Sai1833/Smart-Pill-Box-IoT/01-Simulations/Circuit_Design.jpeg

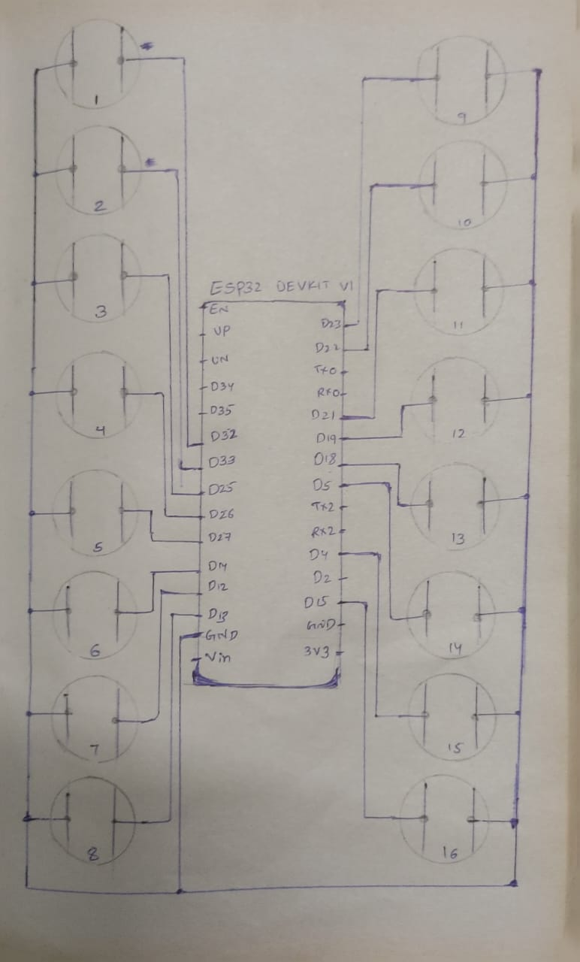
01-Simulations/Circuit_Design.jpeg
