Sai1833/Smart-Pill-Box-IoT/01-Simulations/IR_Simulation.jpeg

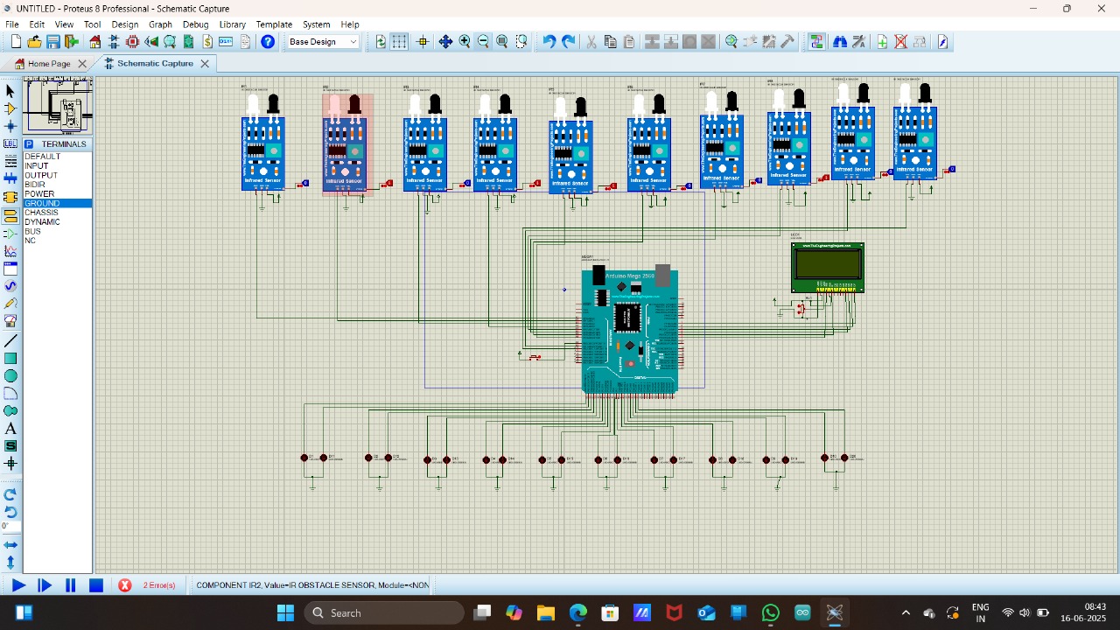
01-Simulations/IR_Simulation.jpeg
