Sai1833/Smart-Pill-Box-IoT/01-Simulations/Touch_Sensor_Simulation.jpeg

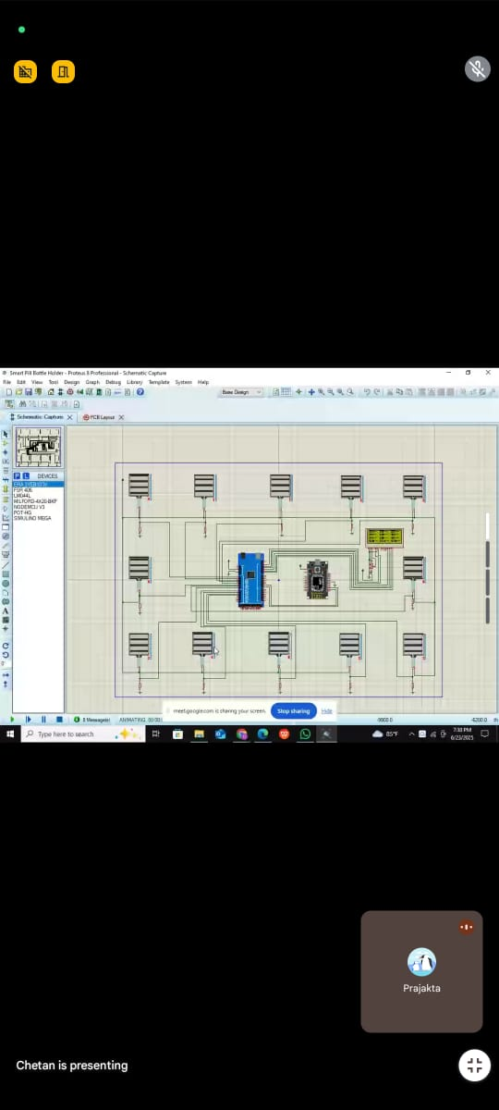
01-Simulations/Touch_Sensor_Simulation.jpeg
