Sai1833/Smart-Pill-Box-IoT/02-Prototype/Cardboard_prototype_1.jpeg

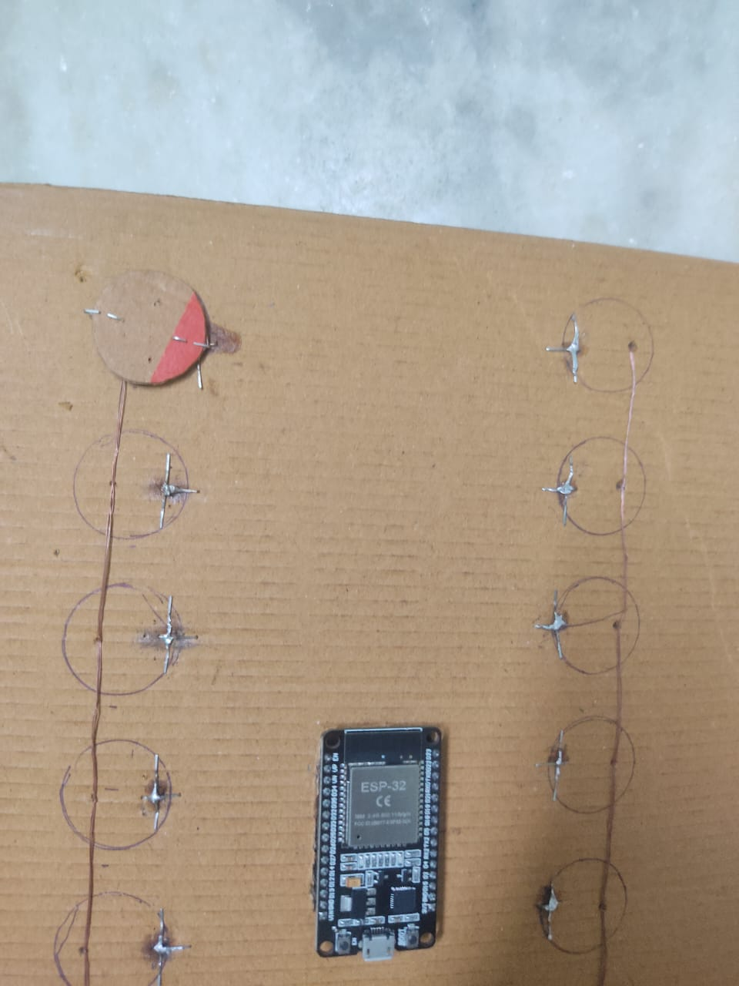
02-Prototype/Cardboard_prototype_1.jpeg
