Sai1833/Smart-Pill-Box-IoT/02-Prototype/Cardboard_prototype_2.jpeg

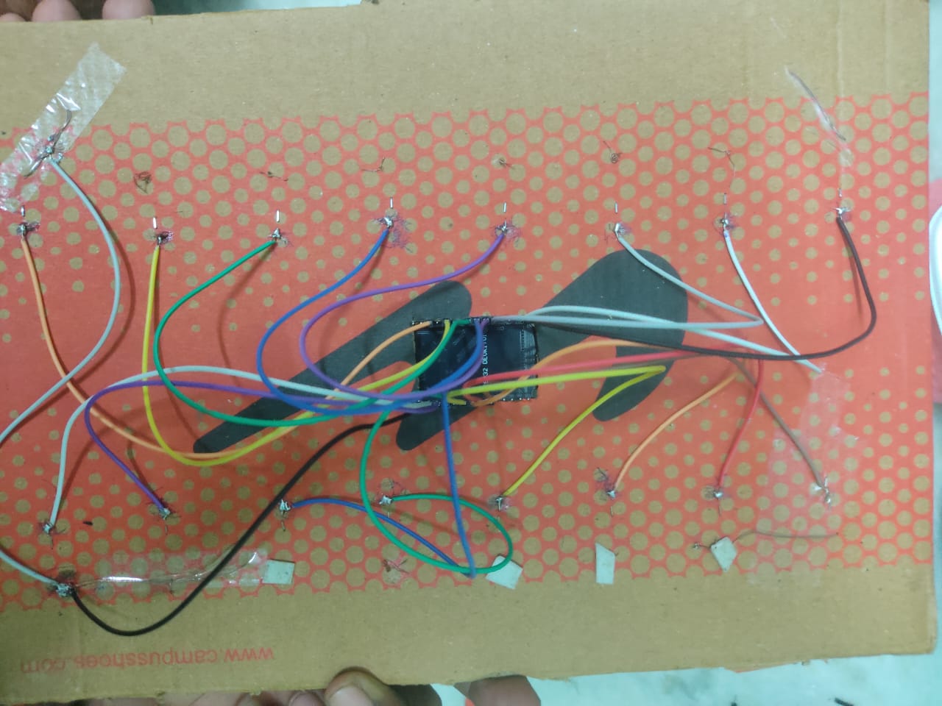
02-Prototype/Cardboard_prototype_2.jpeg
