Sai1833/Smart-Pill-Box-IoT/02-Prototype/Prototype_output.jpeg

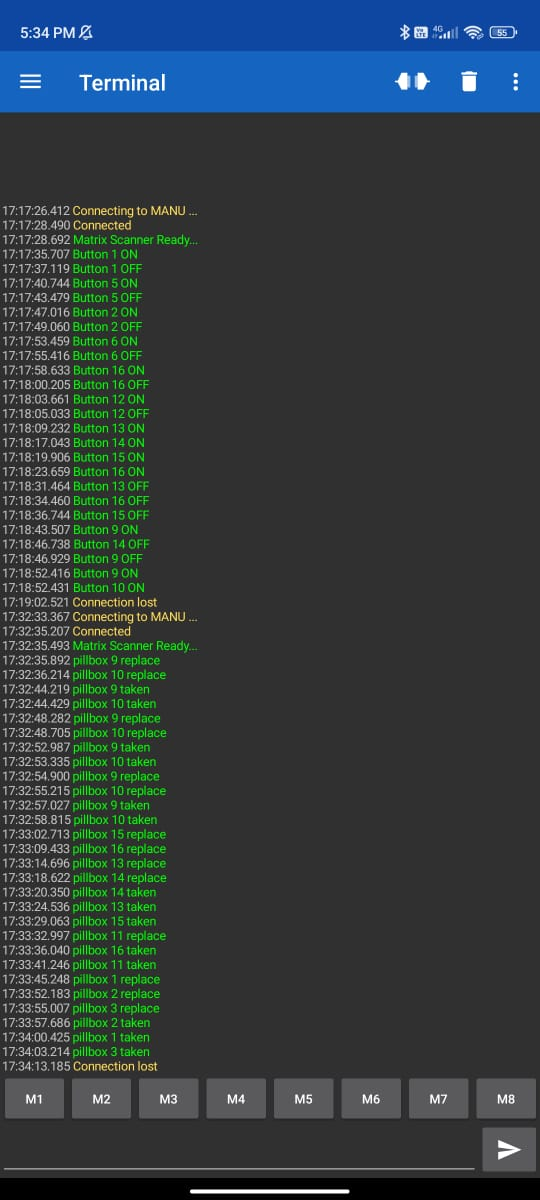
02-Prototype/Prototype_output.jpeg
