Sai1833/Smart-Pill-Box-IoT/02-Prototype/Reference_model.jpeg

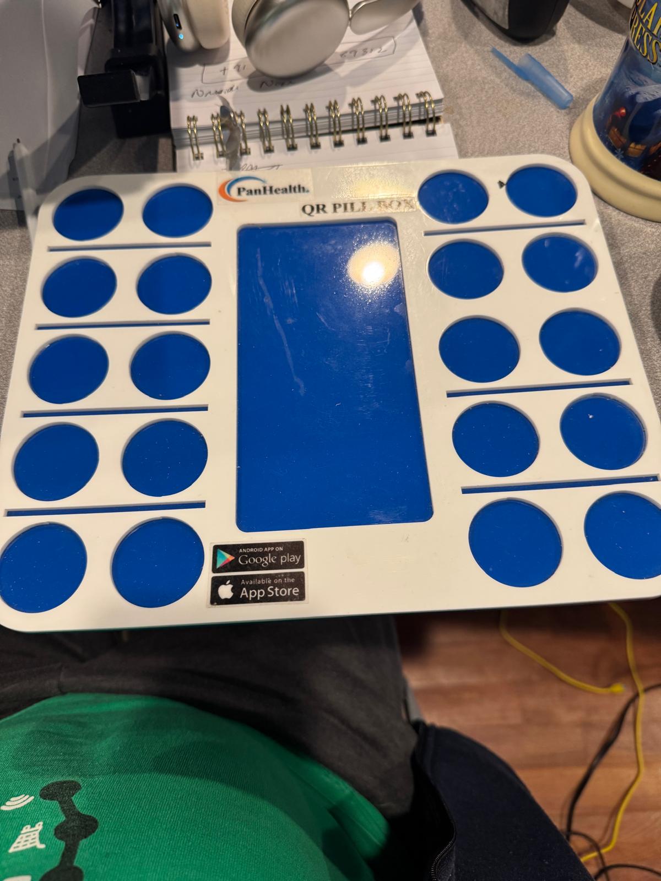
02-Prototype/Reference_model.jpeg
