Sai1833/Smart-Pill-Box-IoT/03-PCB_Design/PCB_Hardware/FeCl3_Mixing_img01.jpg

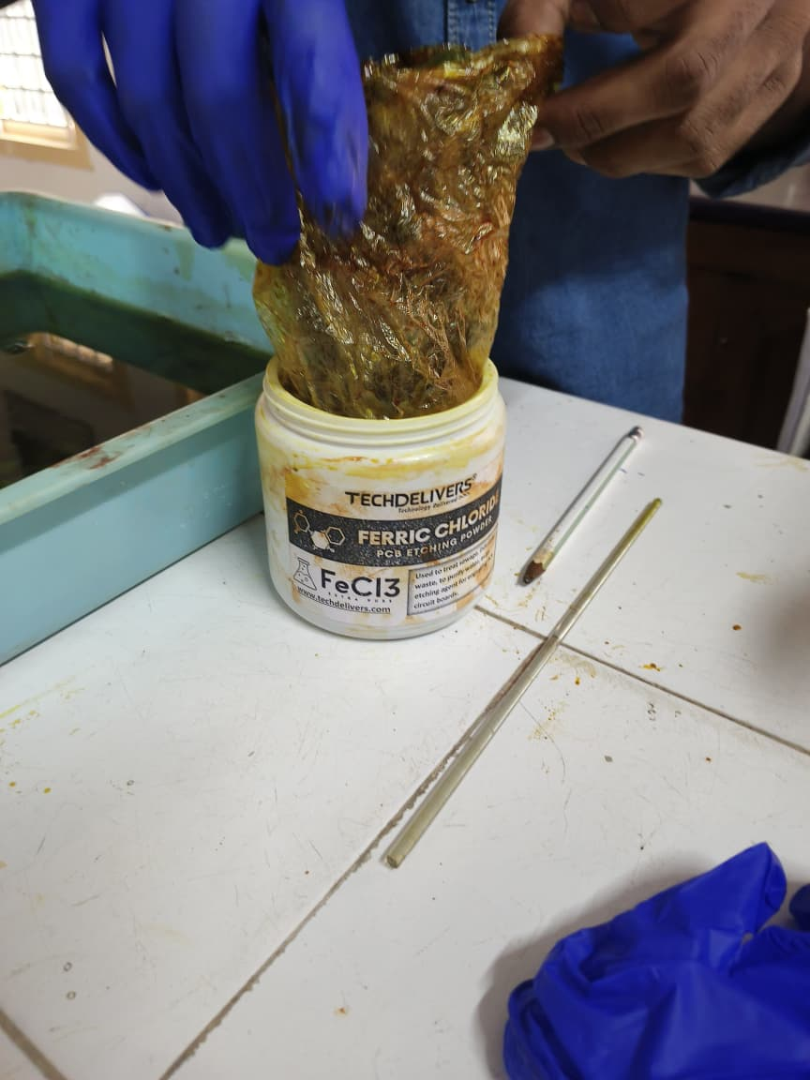
03-PCB_Design/PCB_Hardware/FeCl3_Mixing_img01.jpg
