Sai1833/Smart-Pill-Box-IoT/03-PCB_Design/PCB_Hardware/PCB_Before_Removing_Copper_img01.jpg

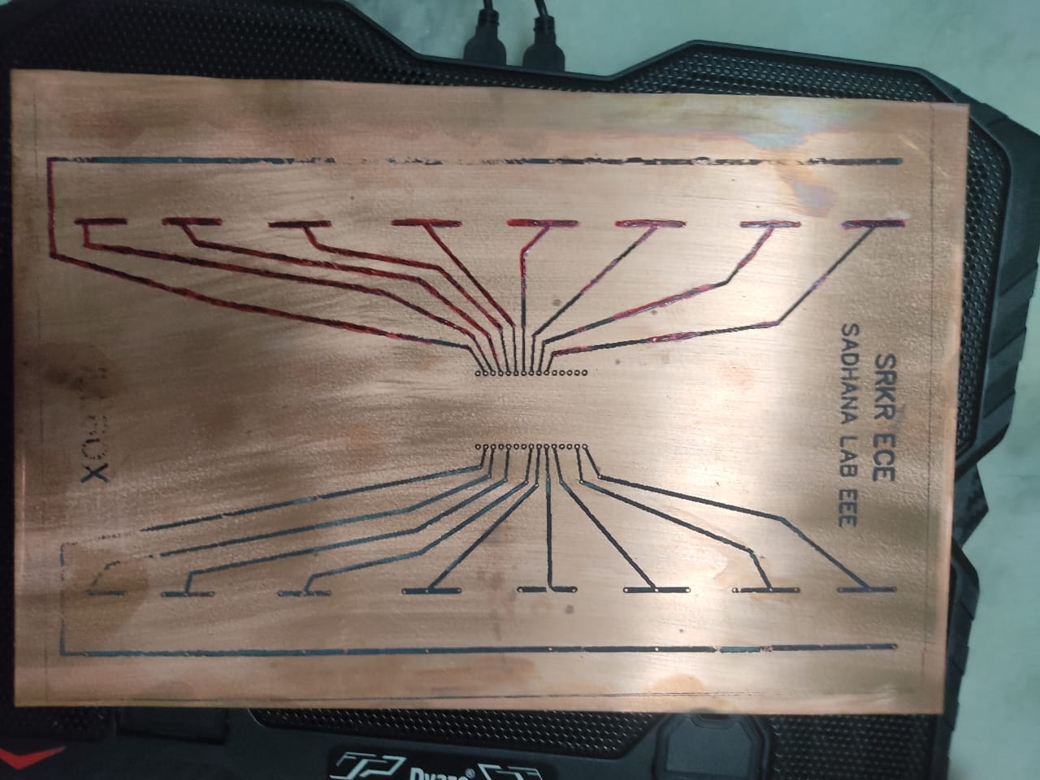
03-PCB_Design/PCB_Hardware/PCB_Before_Removing_Copper_img01.jpg
