Sai1833/Smart-Pill-Box-IoT/03-PCB_Design/PCB_Hardware/PCB_with_Sholdered_MC_img03.jpg

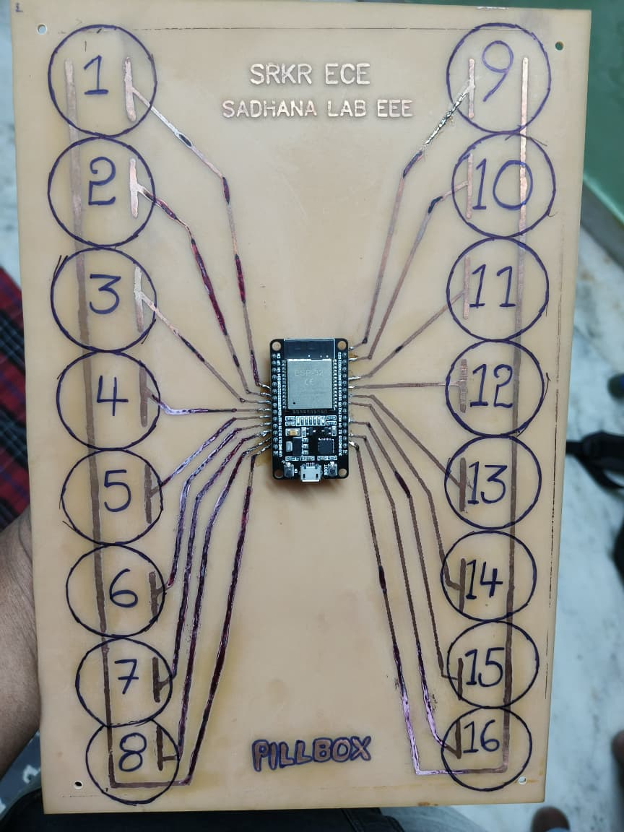
03-PCB_Design/PCB_Hardware/PCB_with_Sholdered_MC_img03.jpg
