Sai1833/Smart-Pill-Box-IoT/03-PCB_Design/PCB_Simulation/PCB_Design_EasyEda_img02.jpg

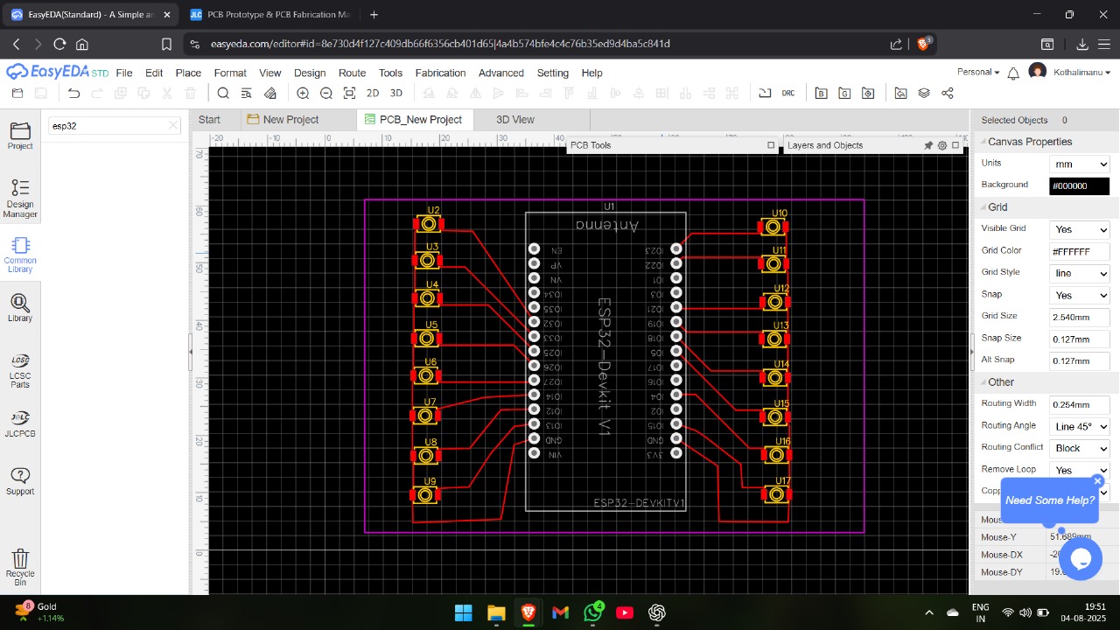
03-PCB_Design/PCB_Simulation/PCB_Design_EasyEda_img02.jpg
