Sai1833/Smart-Pill-Box-IoT/04-3D_Design/Autocad_3D_Design_Top&Bottle_img01.jpg

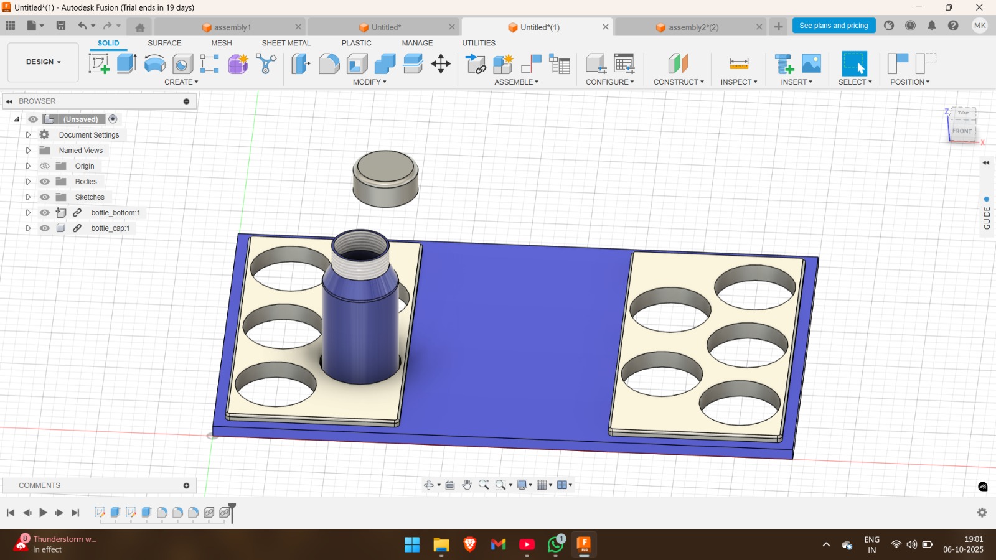
04-3D_Design/Autocad_3D_Design_Top&Bottle_img01.jpg
