Sai1833/Smart-Pill-Box-IoT/04-3D_Design/Autocad_3D_Design_Top_img02.jpg

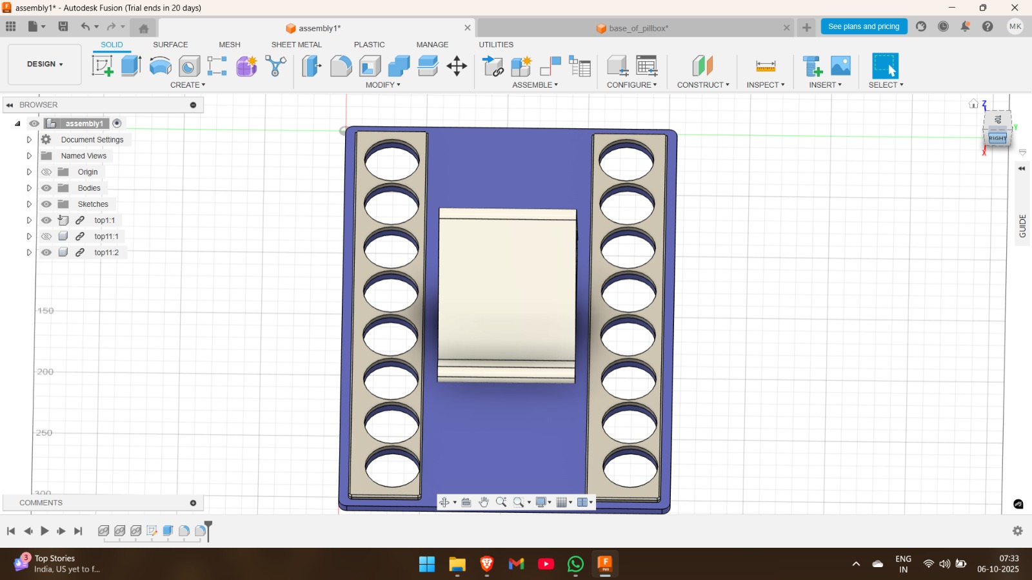
04-3D_Design/Autocad_3D_Design_Top_img02.jpg
