Sai1833/Smart-Pill-Box-IoT/05-Final_output/Final_Output_Insidebox_img03.jpg

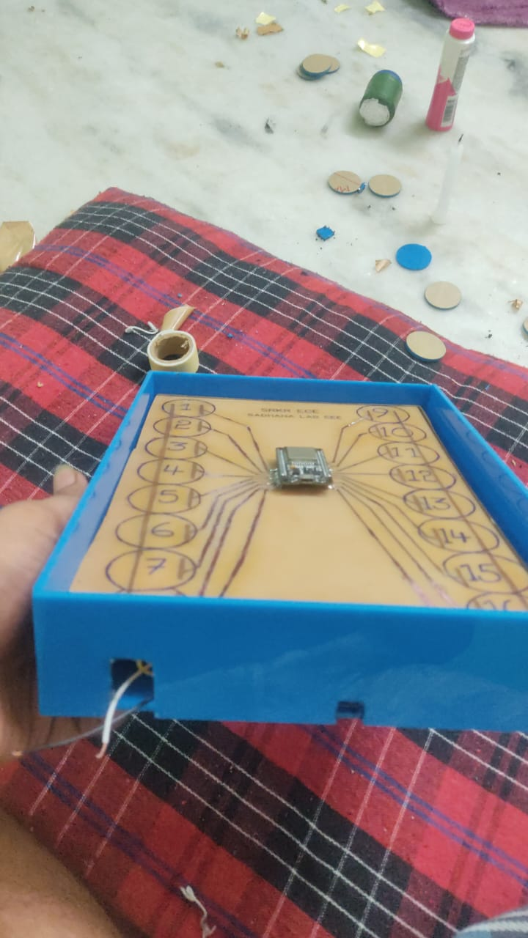
05-Final_output/Final_Output_Insidebox_img03.jpg
