Sai1833/Smart-Pill-Box-IoT/05-Final_output/Outlet_Box_Laser_Cutting_img01.jpg

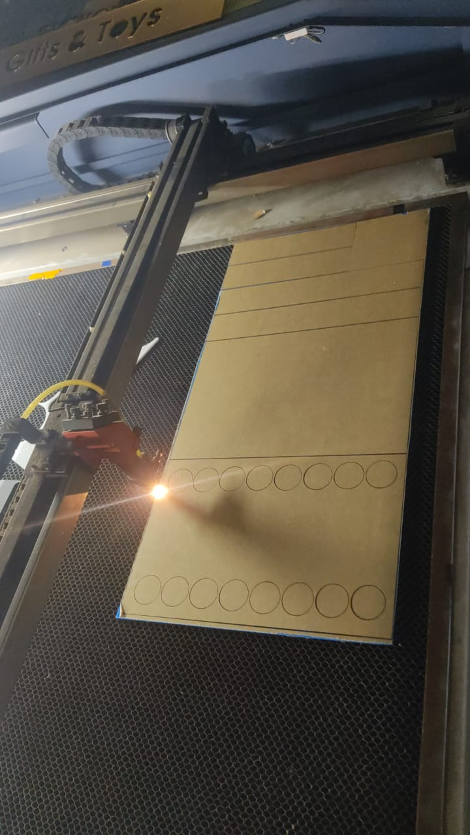
05-Final_output/Outlet_Box_Laser_Cutting_img01.jpg
