Sai1833/Smart-Pill-Box-IoT/03-PCB_Design/PCB_Simulation/PCB_Design_Printout_img04.jpg

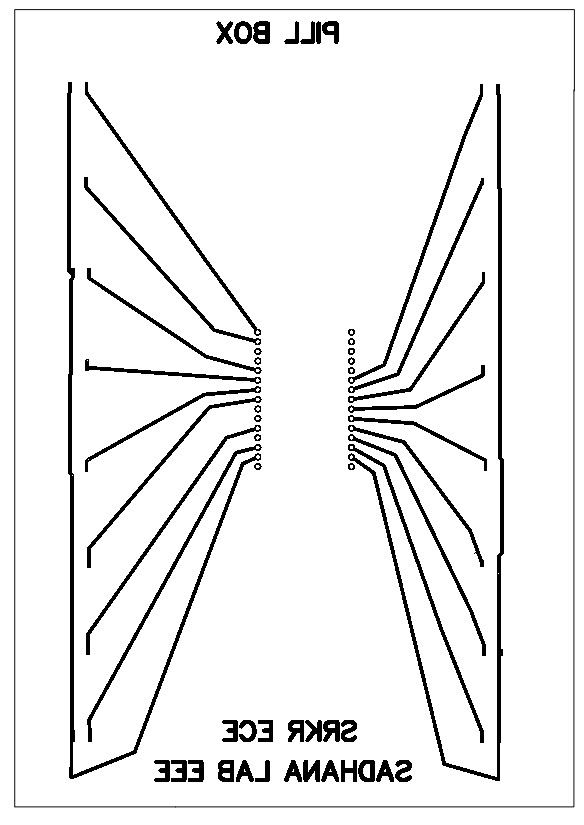
03-PCB_Design/PCB_Simulation/PCB_Design_Printout_img04.jpg
